Archive-663/nikonF/ASSETS/PHOTO/SAMPLE/INSTA/INSTA-1.jpg

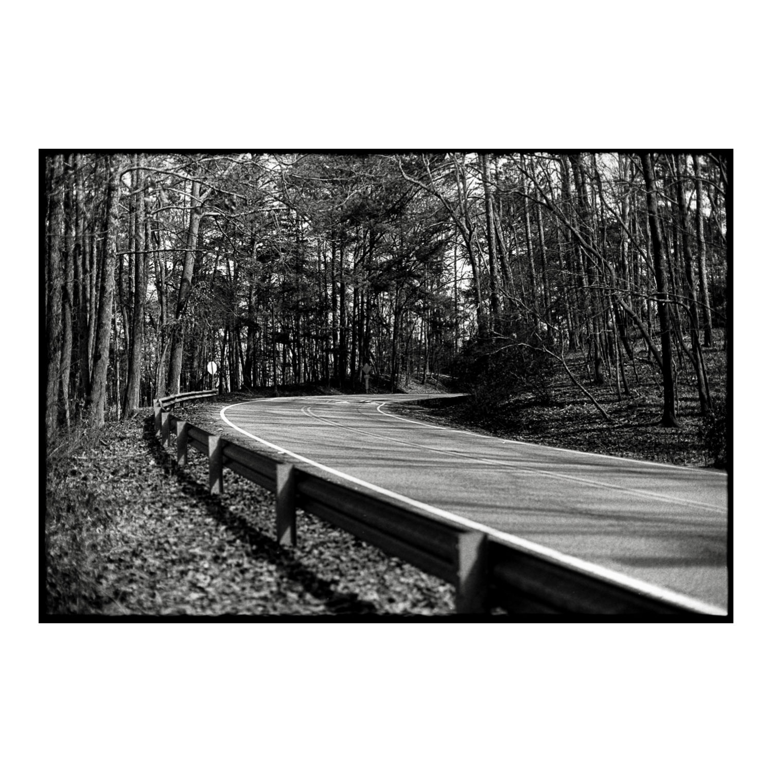
ASSETS/PHOTO/SAMPLE/INSTA/INSTA-1.jpg
