Archive-663/nikonF/ASSETS/PHOTO/SAMPLE/INSTA/INSTA-2.jpg

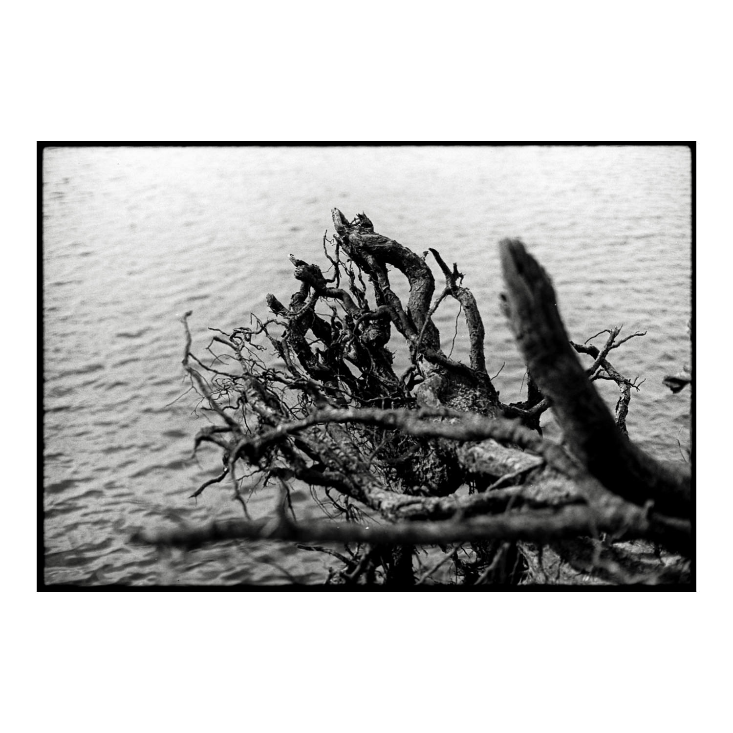
ASSETS/PHOTO/SAMPLE/INSTA/INSTA-2.jpg
