Archive-663/nikonF/ASSETS/PHOTO/SAMPLE/nikonF_viewFinders_sample (1).jpg

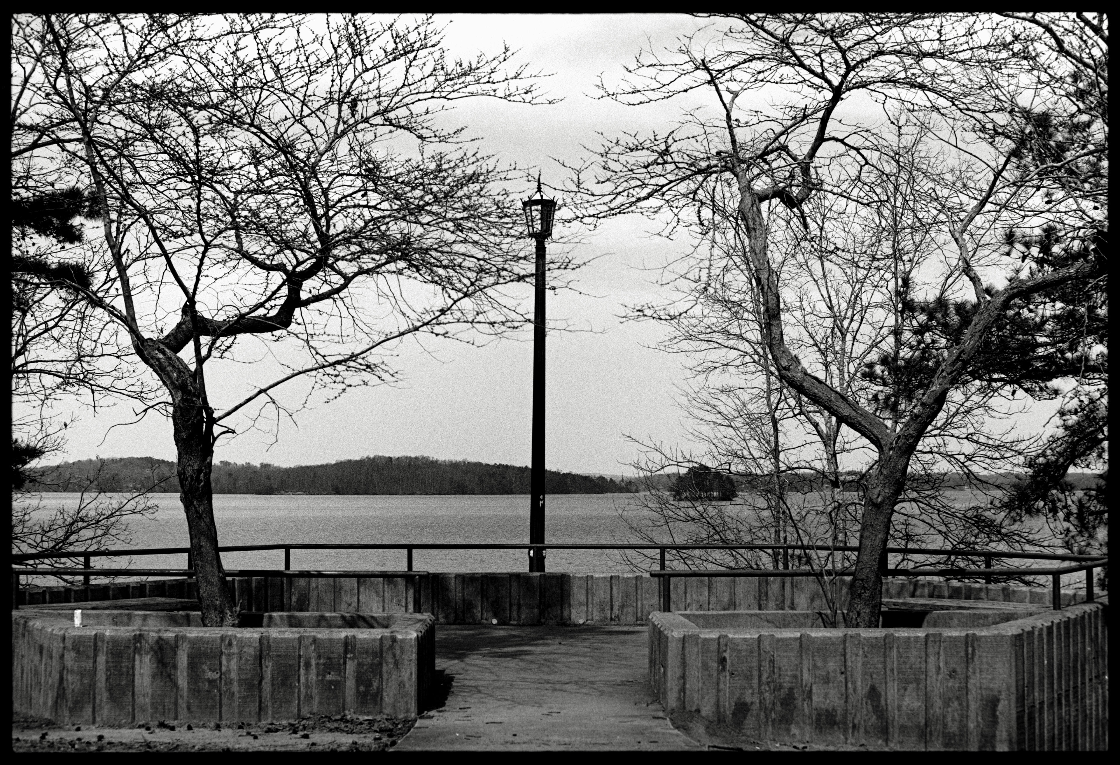
ASSETS/PHOTO/SAMPLE/nikonF_viewFinders_sample (1).jpg
