Archive-663/nikonF/ASSETS/PHOTO/SAMPLE/nikonF_viewFinders_sample (18).jpg

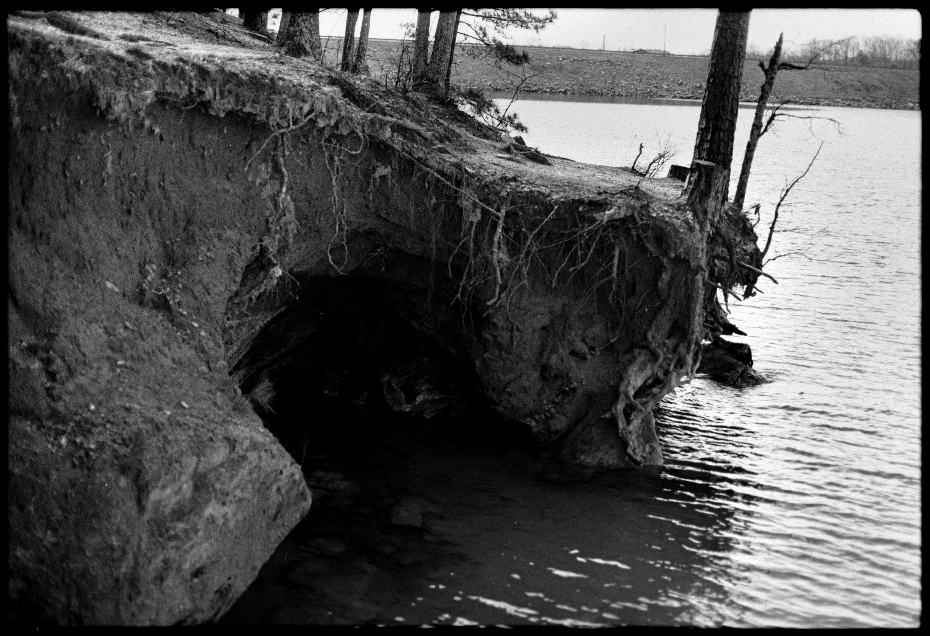
ASSETS/PHOTO/SAMPLE/nikonF_viewFinders_sample (18).jpg
